wangdrew/light-switch/media/img1.jpg

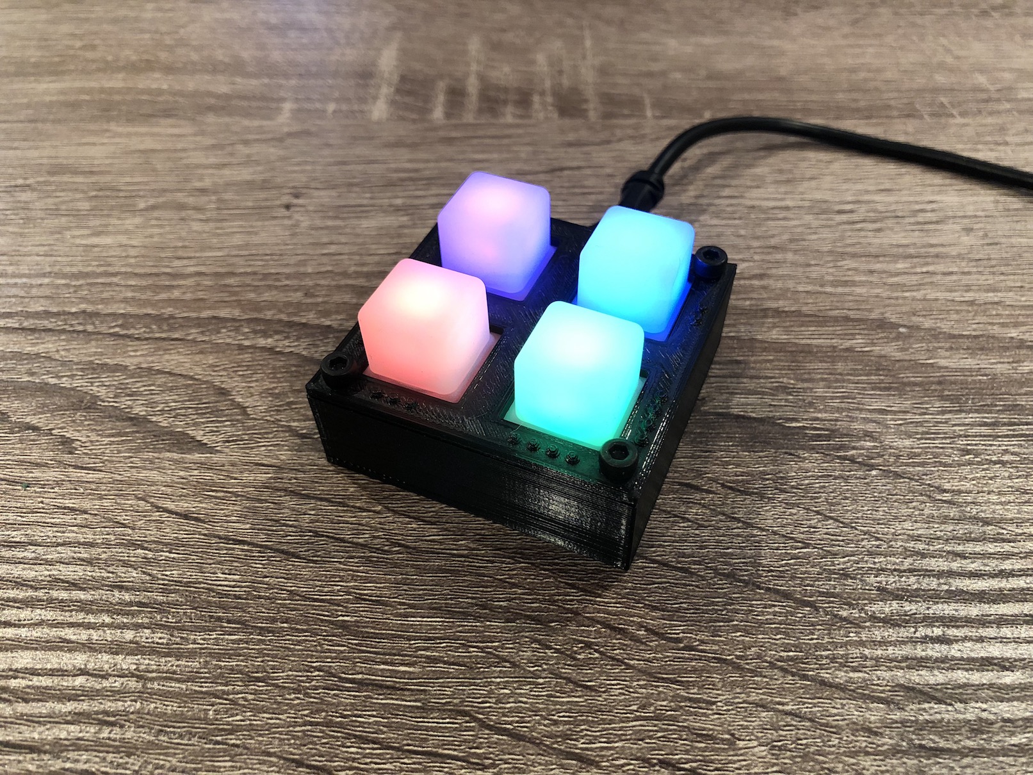
media/img1.jpg
