wangdrew/light-switch/media/img2.jpg

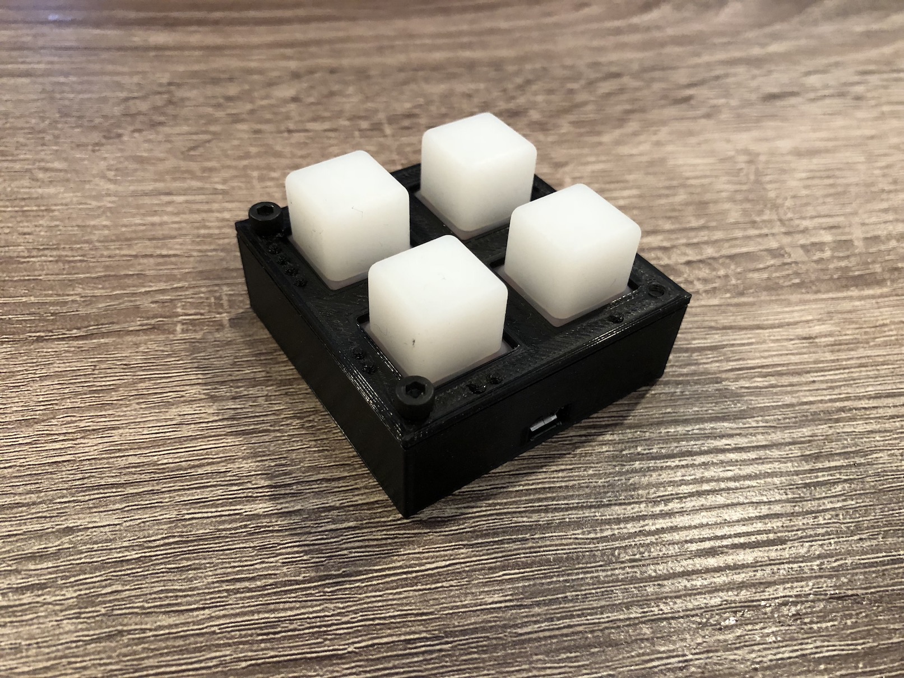
media/img2.jpg
