wangdrew/light-switch/media/img3.jpg

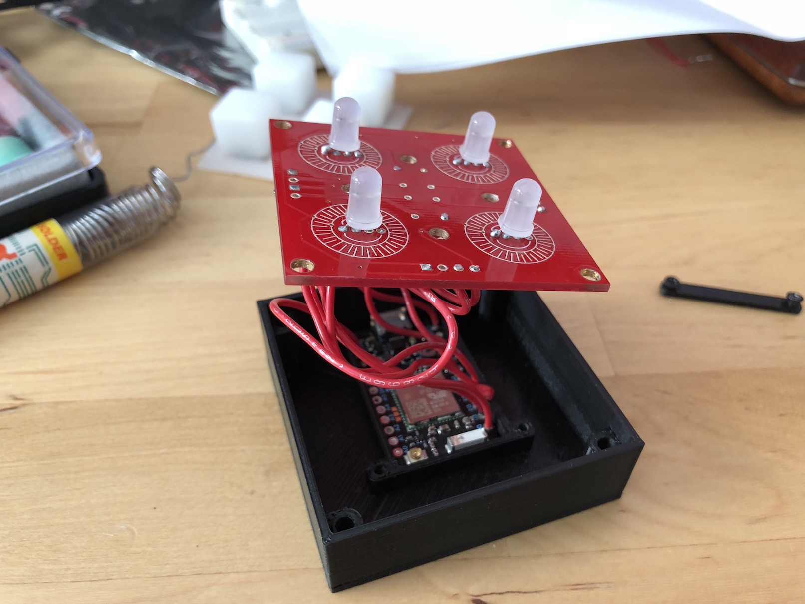
media/img3.jpg
